LaskaKit/ESPwled/img/13115-2.jpg

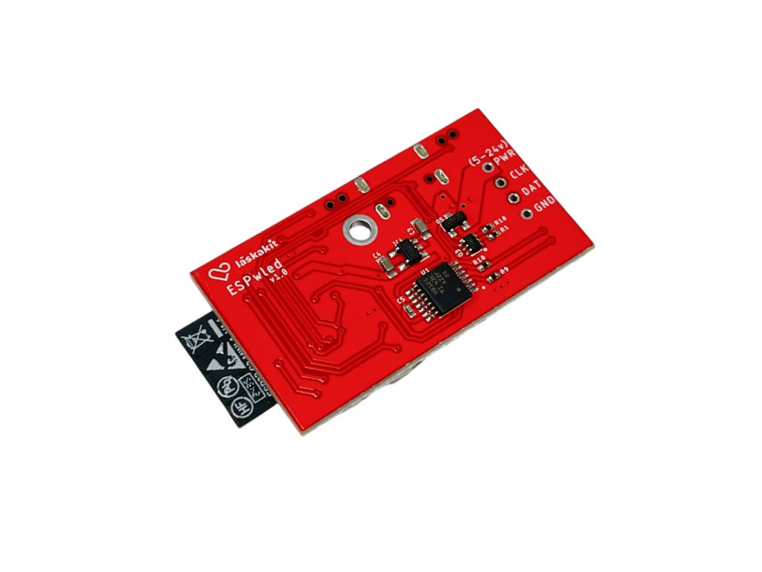
img/13115-2.jpg
