LaskaKit/ESPwled/img/13115-4.jpg

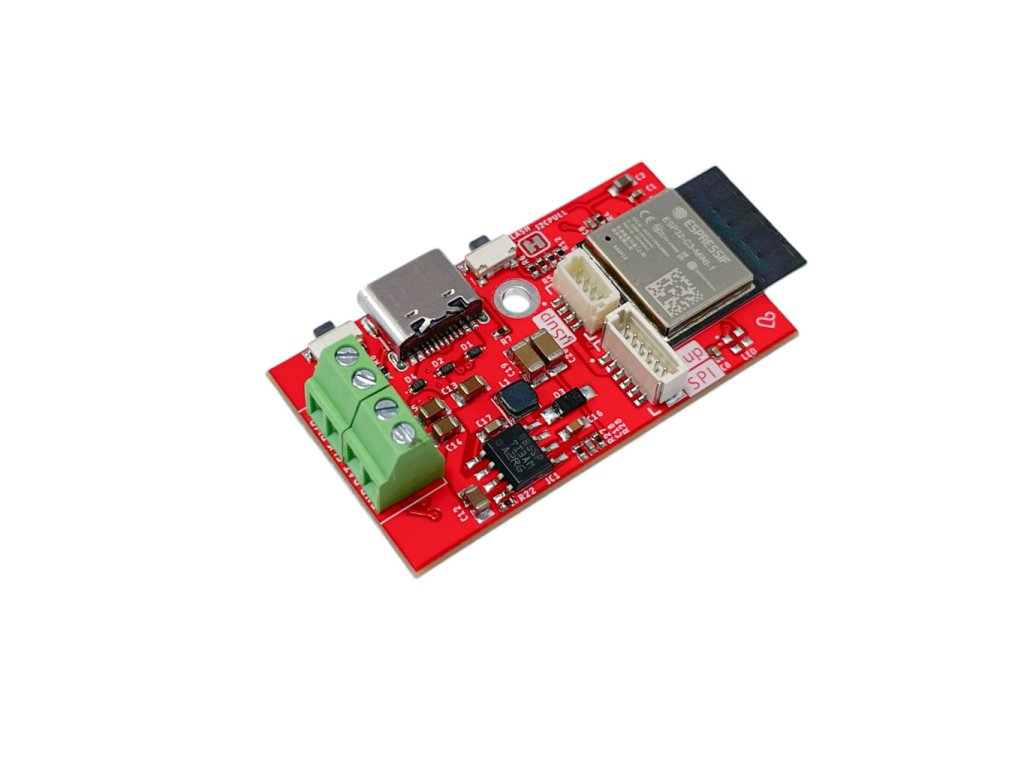
img/13115-4.jpg
