LaskaKit/ESPwled/img/13115.jpg

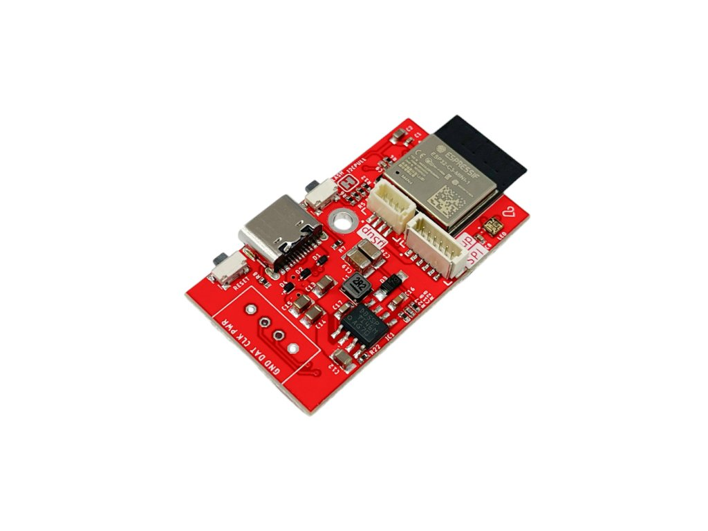
img/13115.jpg
